nvitya/minimal_boards/mibo20_stm32/output/MIBO20-Front.png

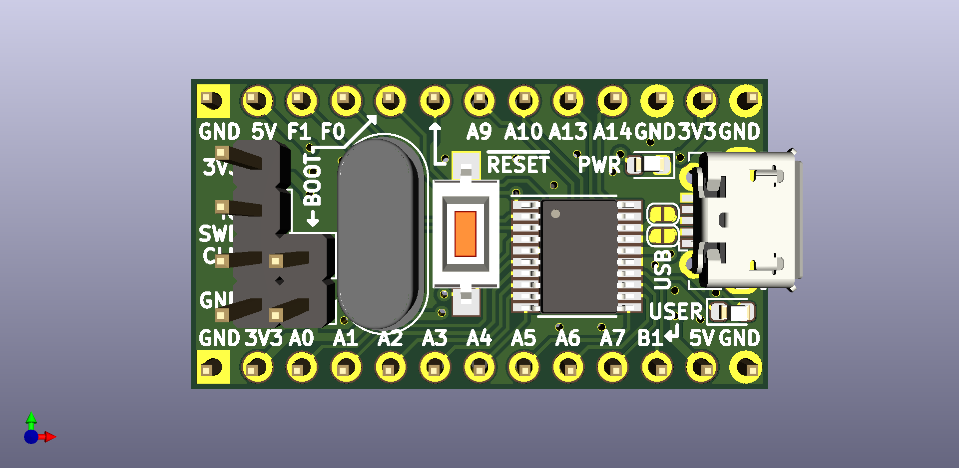
mibo20_stm32/output/MIBO20-Front.png
