nvitya/minimal_boards/mibo20_stm32/output/MIBO-Back.png

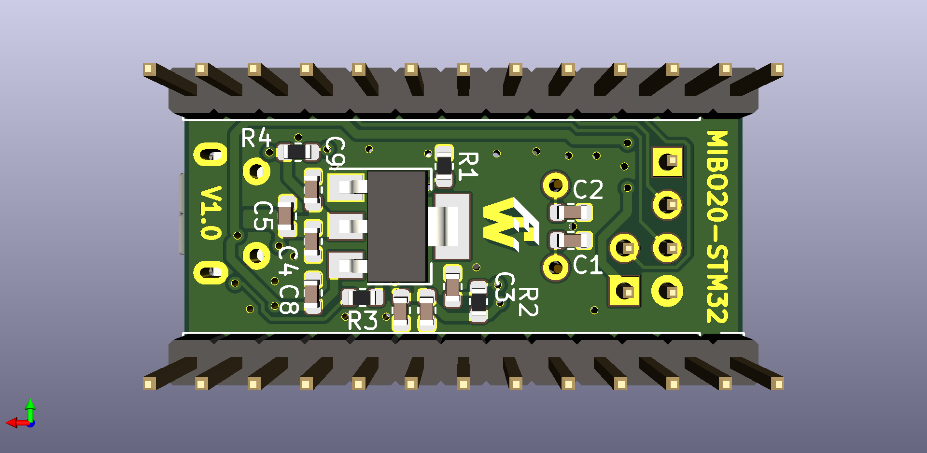
mibo20_stm32/output/MIBO-Back.png
